michalcourson/Harmonizer/design/assembly_images/Harmonizer_assembled_PCB.png

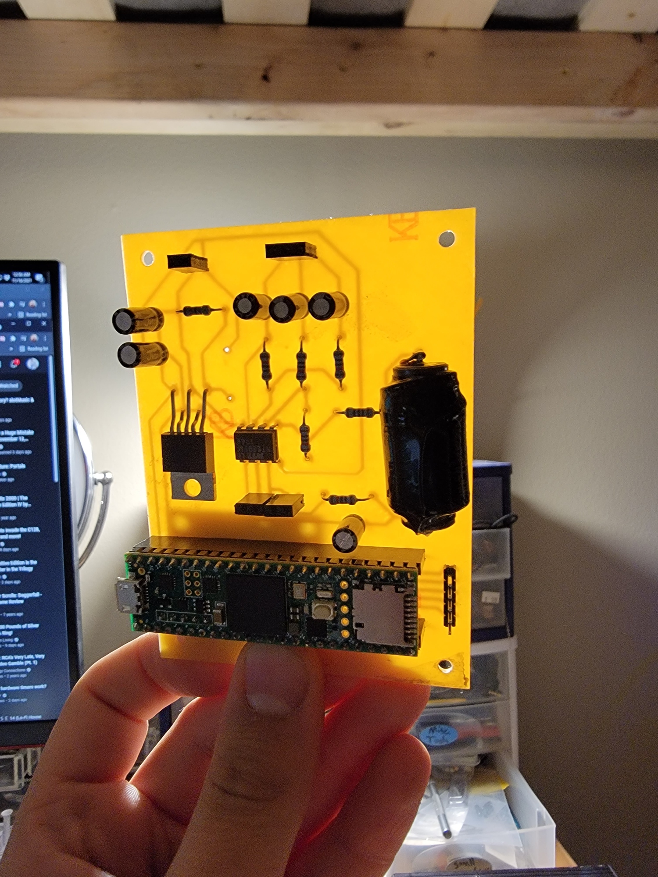
design/assembly_images/Harmonizer_assembled_PCB.png
