michalcourson/Harmonizer/design/assembly_images/Harmonizer_rear.png

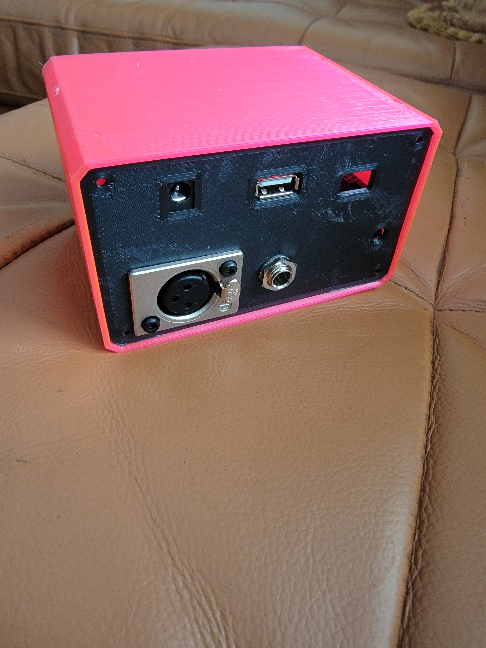
design/assembly_images/Harmonizer_rear.png
