michalcourson/Harmonizer/data/figures/pv_monophonic_test_results.png

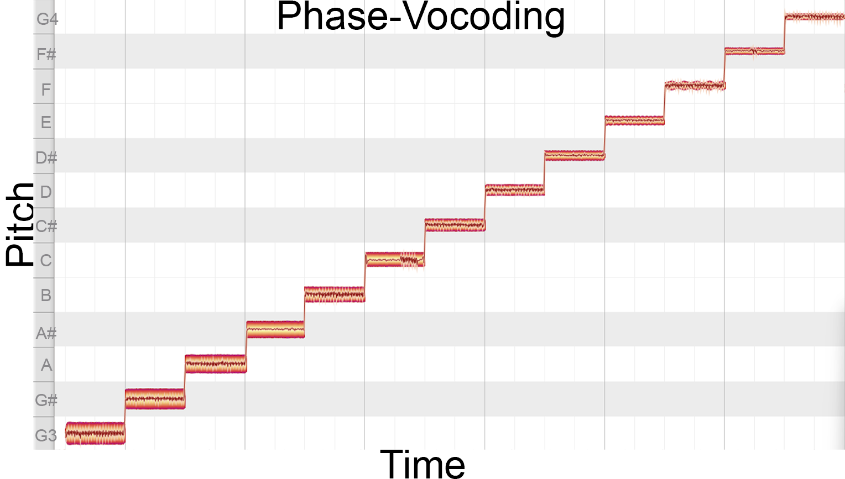
data/figures/pv_monophonic_test_results.png
