michalcourson/Harmonizer/data/figures/pv_timing_results.png

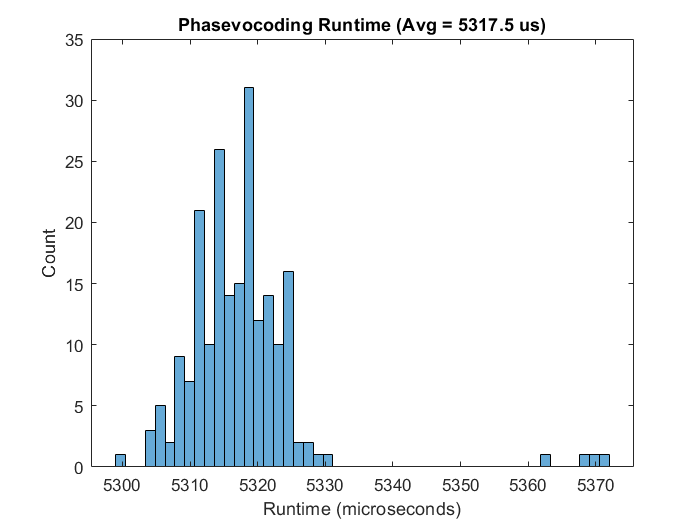
data/figures/pv_timing_results.png
