michalcourson/Harmonizer/data/figures/td_psola_monophonic_test_results.png

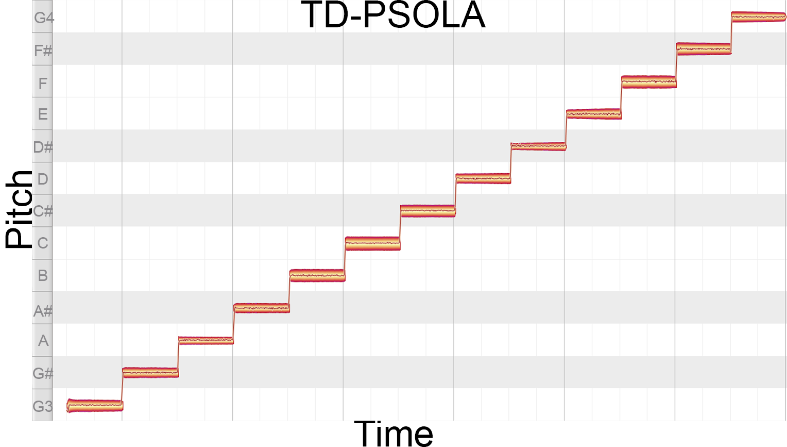
data/figures/td_psola_monophonic_test_results.png
