michalcourson/Harmonizer/data/figures/td_psola_timing_results.png

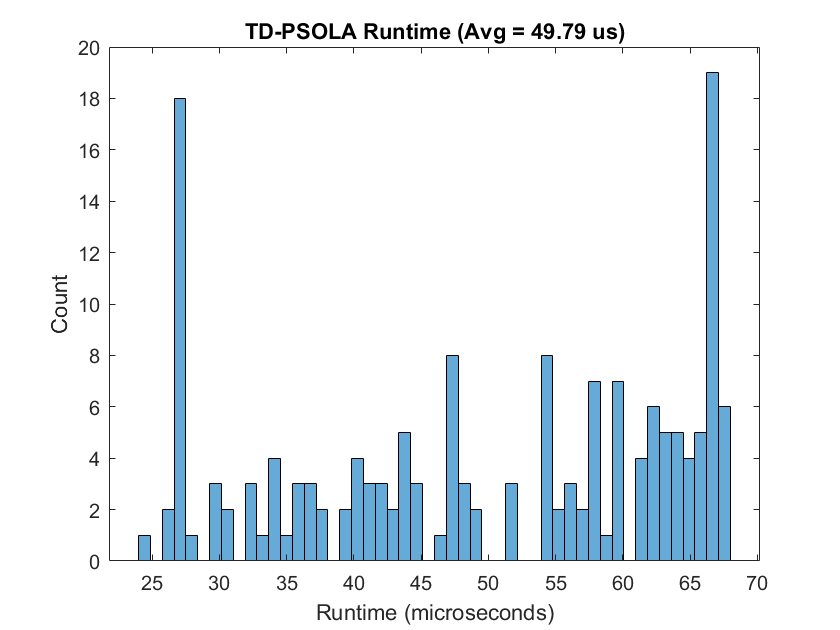
data/figures/td_psola_timing_results.png
