michalcourson/Harmonizer/data/figures/tritonal_stft_test_results.png

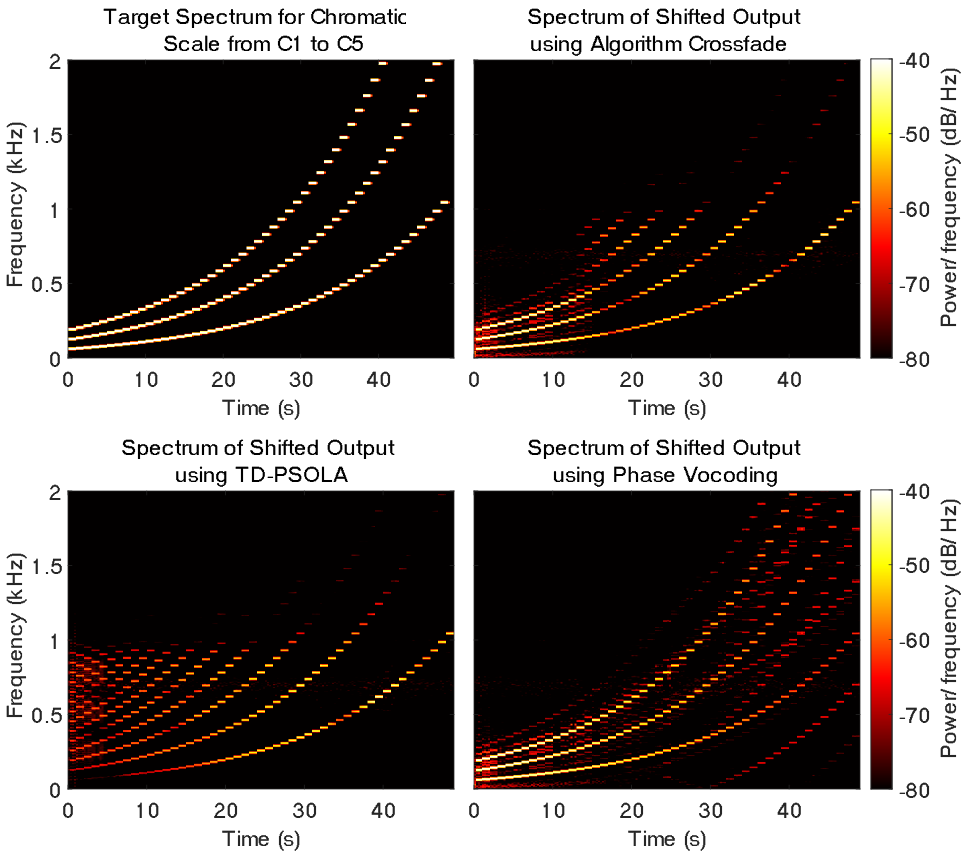
data/figures/tritonal_stft_test_results.png
