michalcourson/Harmonizer/design/PCB_design/ltspice_simulation.asc

B2: bv; V=12
C1: cap; 100µ
C2: cap; 100µ
C3: cap; 1µ
C4: cap; 1µ
C10: cap; .22µ
L1: ind; 500µ
R1: res; 1k
R2: res; 47k
R3: res; 100
R4: res; 1k
R5: res; 33k
R6: res; 10k
R7: res; 10k
R13: res; 10k
R14: res; 10k
R15: res; 10k
R16: res; 10k
U1: UniversalOpamp2
U2: UniversalOpamp2
U3: UniversalOpamp2
U5: opamp
V2: voltage; AC 1
Named nets: VP, 0, VN, Vout, Vsig, Vinv, vgnd
.lib opamp.sub
.ac dec 100 20 100k
